svartalfarqc/arduino-drumkit/Arduino_Drumkit_2026/20260524_154737.jpg

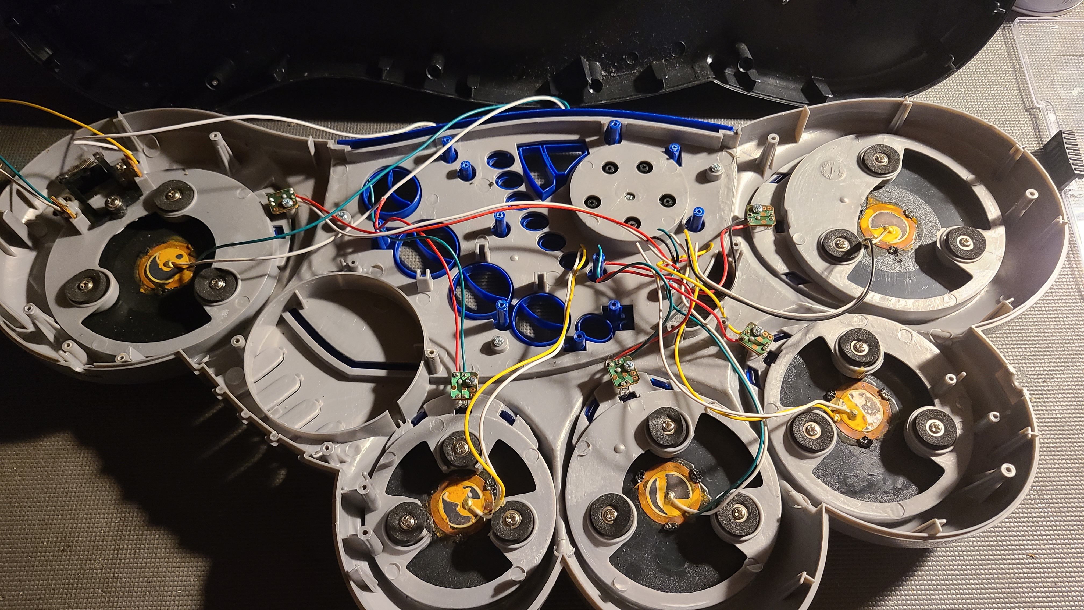
Arduino_Drumkit_2026/20260524_154737.jpg
