svartalfarqc/arduino-drumkit/Arduino_Drumkit_2026/20260524_154746.jpg

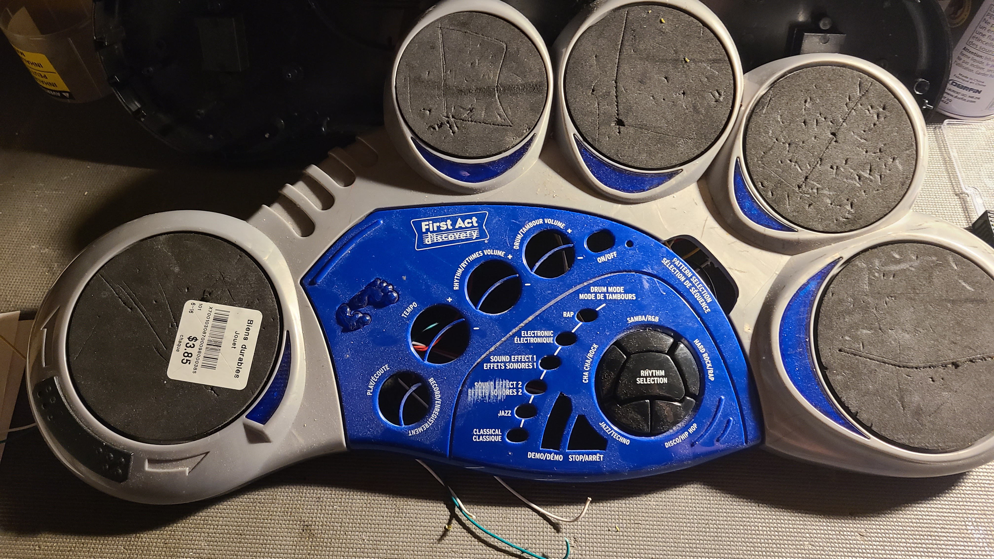
Arduino_Drumkit_2026/20260524_154746.jpg
