svartalfarqc/arduino-drumkit/Arduino_Drumkit_2026/20260524_154820.jpg

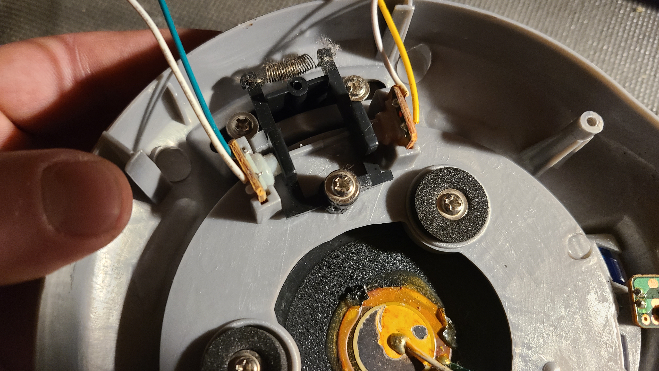
Arduino_Drumkit_2026/20260524_154820.jpg
